maximvoven/Hydrophone-Amplifier-Oizys/LTspiceXVII/AmpV0.asc

C1: cap; 1.6nf
C2: cap; 330pF
C3: cap; 3.3nf
C4: cap; 10µf
R1: res; 1G
R2: res; 1k
R3: res; 330
R4: res; 22k
R5: res; 10k
R6: res; 680
R7: res; 1.2k
R8: res; 190
Stage_1: AD8676_A
Stage_2: AD8676_A
U1: AD8676_A
V1: voltage; SINE(0 0.4 40k); AC 0.4
V3: voltage; 12
V4: voltage; 12
Named nets: 0, -12V, 12v, 12V, 1.6v
;ac dec 100 1k 200k
.tran 0 0.001 0 startup
Copyright (c) 2020 Maxim Vovenko
 
Software is hereby stated to be any and all digital files needed to produce a 
physical product as described by these digital files.
 
Permission is hereby granted, free of charge, to any person obtaining a copy
of this software and associated documentation files (the "Software"), to deal
in the Software without restriction, including without limitation the rights
to use, copy, modify, merge, publish, distribute, sublicense, and/or sell
copies of the Software, and to permit persons to whom the Software is
furnished to do so, subject to the following conditions:
 
The above copyright notice and this permission notice shall be included in all
copies or substantial portions of the Software.
 
THE SOFTWARE IS PROVIDED "AS IS", WITHOUT WARRANTY OF ANY KIND, EXPRESS OR
IMPLIED, INCLUDING BUT NOT LIMITED TO THE WARRANTIES OF MERCHANTABILITY,
FITNESS FOR A PARTICULAR PURPOSE AND NONINFRINGEMENT. IN NO EVENT SHALL THE
AUTHORS OR COPYRIGHT HOLDERS BE LIABLE FOR ANY CLAIM, DAMAGES OR OTHER
LIABILITY, WHETHER IN AN ACTION OF CONTRACT, TORT OR OTHERWISE, ARISING FROM,
OUT OF OR IN CONNECTION WITH THE SOFTWARE OR THE USE OR OTHER DEALINGS IN THE
SOFTWARE.
